javaBin/PollZone/schematic-v5/pdf/pollbox-Layout.pdf

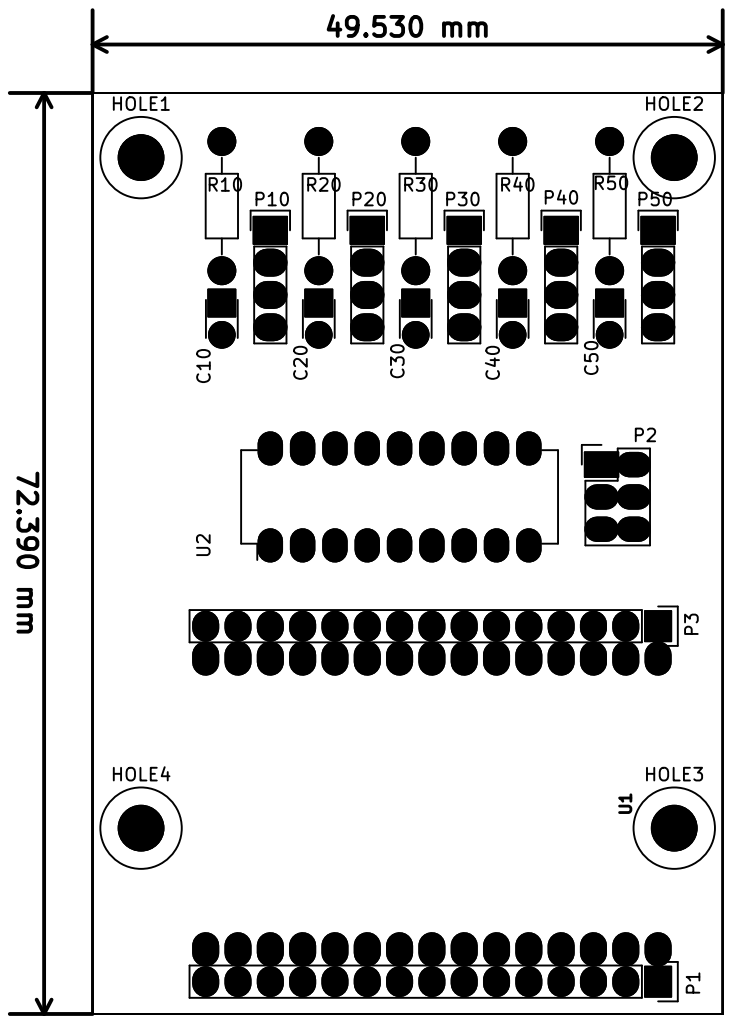
[picture p12: page 1]
