javaBin/PollZone/schematic-v4/pdf/pollbox-Assembly.pdf

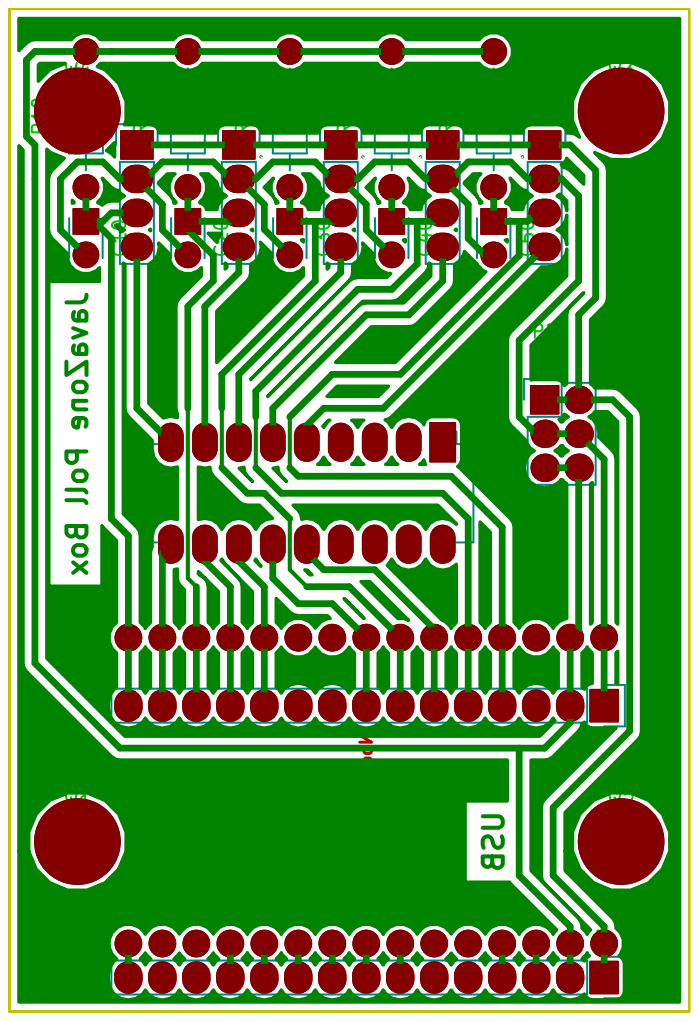
[picture p13: page 1]
