javaBin/PollZone/schematic-v4/pdf/pollbox-AssyOutlinesTop.pdf

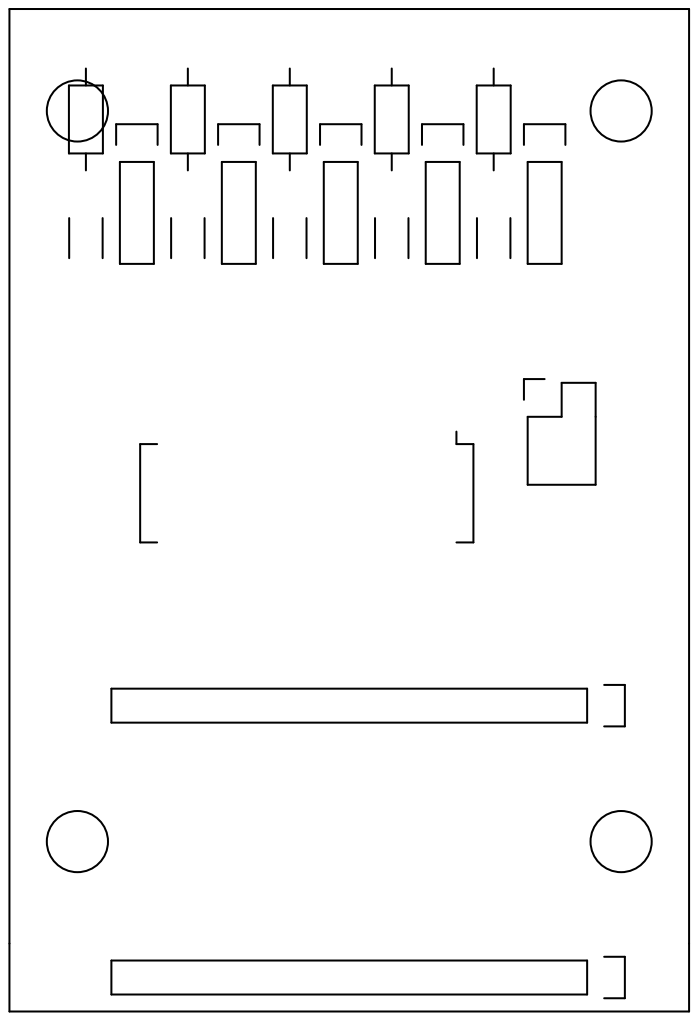
[picture p14: page 1]
