javaBin/PollZone/schematic-v4/pdf/pollbox-AssyTop.pdf

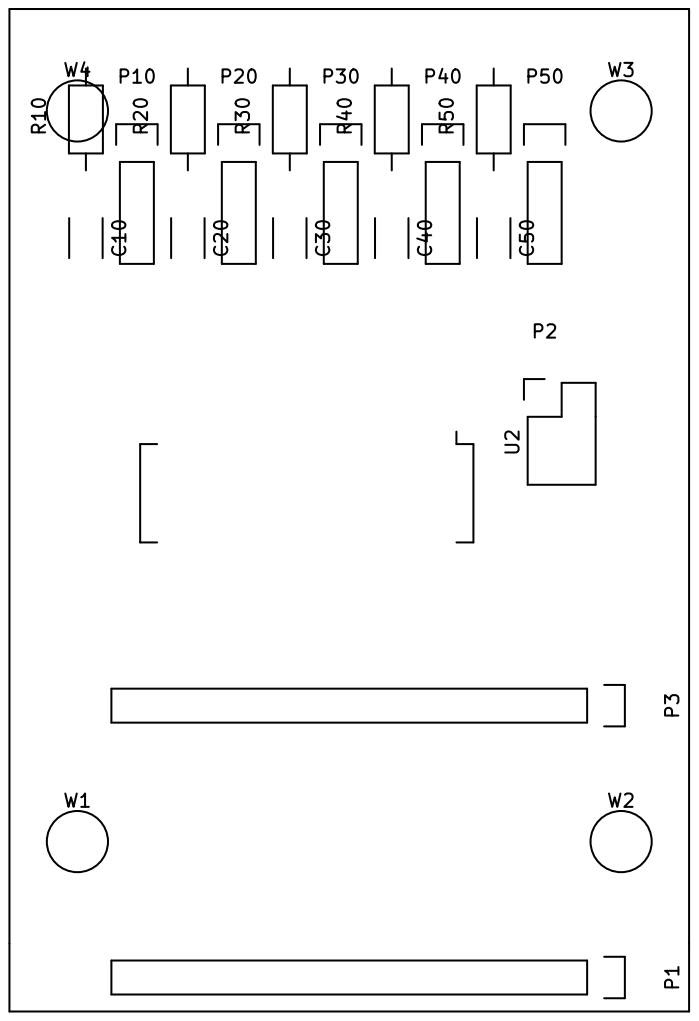
[picture p15: page 1]
