javaBin/PollZone/schematic-v4/pdf/pollbox-B.Cu.pdf

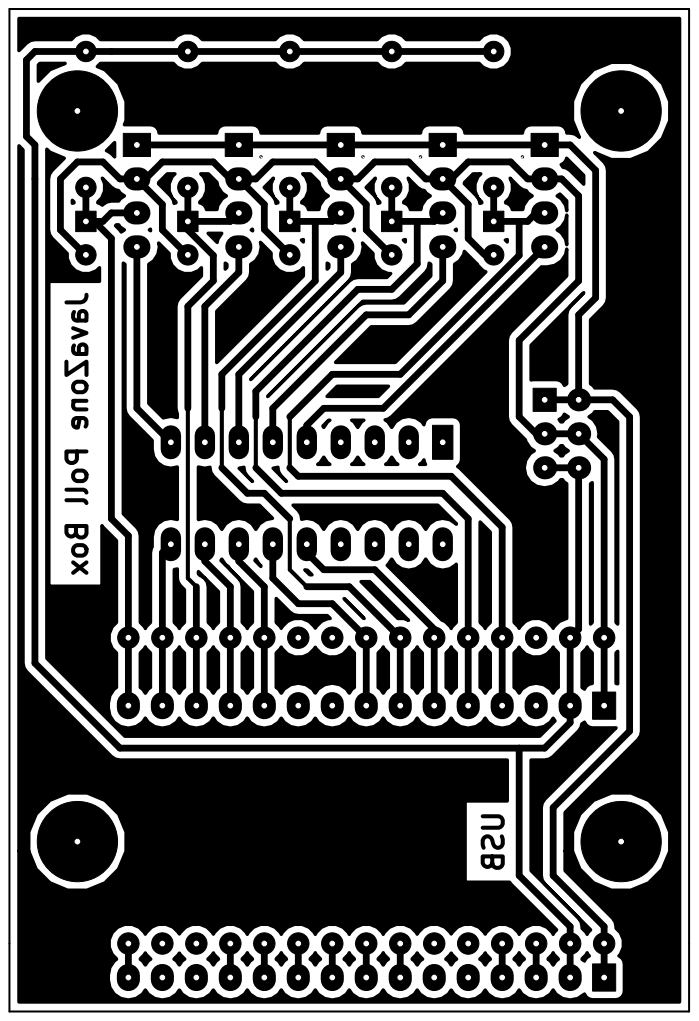
[picture p16: page 1]

USB JavaZone Poll Box
