javaBin/PollZone/schematic-v4/pdf/pollbox-B.Mask.pdf

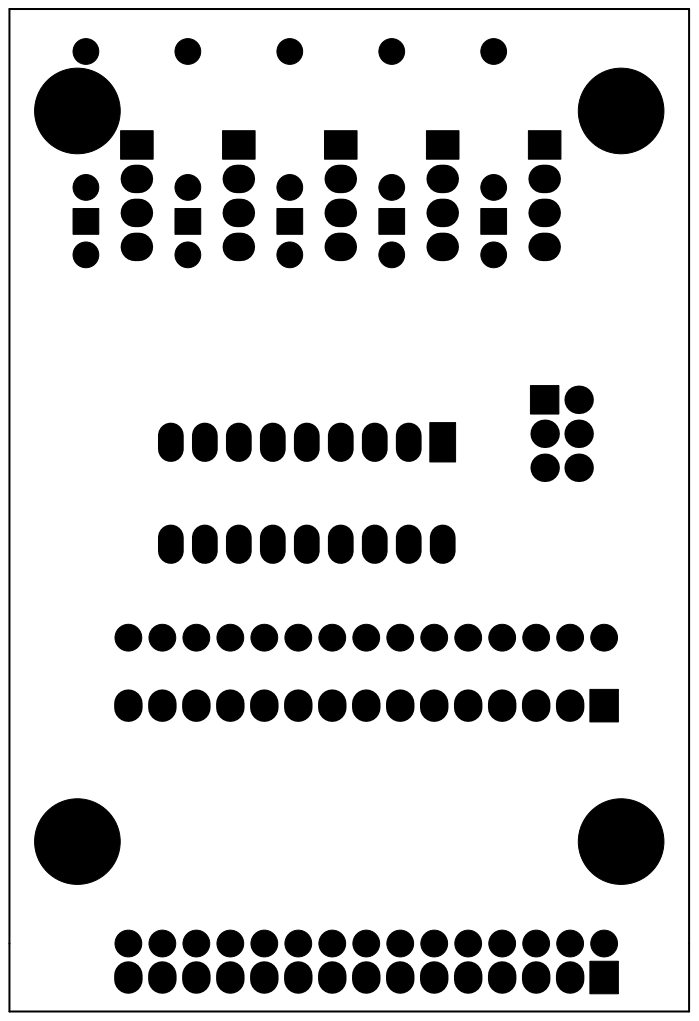
[picture p17: page 1]
