javaBin/PollZone/schematic-v4/pdf/pollbox-B.Silk.pdf

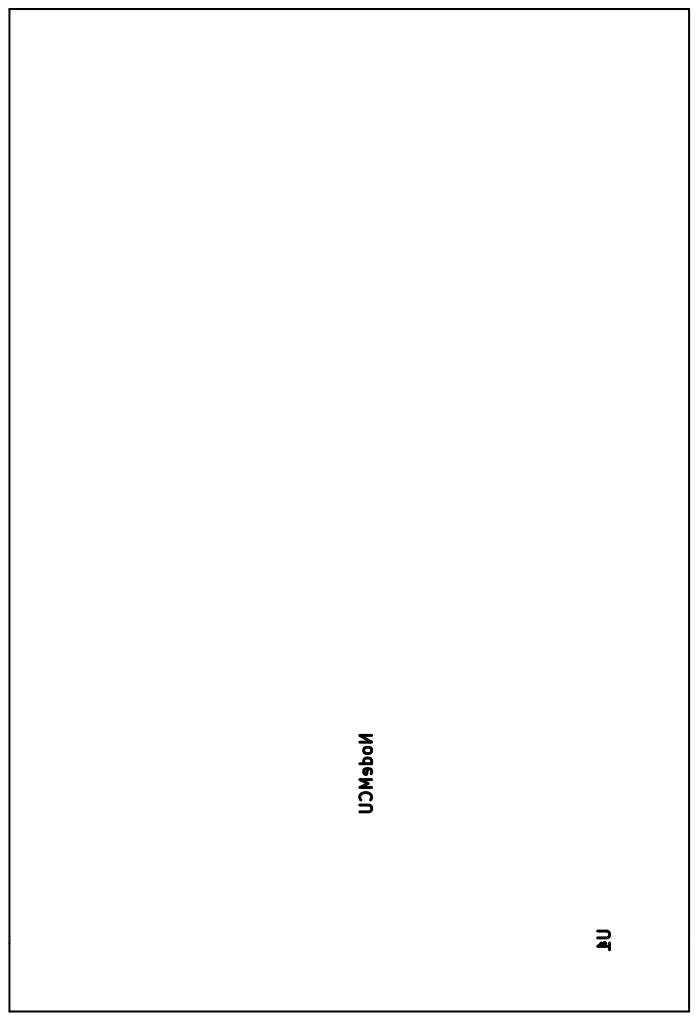
[picture p18: page 1]
