javaBin/PollZone/schematic-v4/pdf/pollbox-Cmts.User.pdf

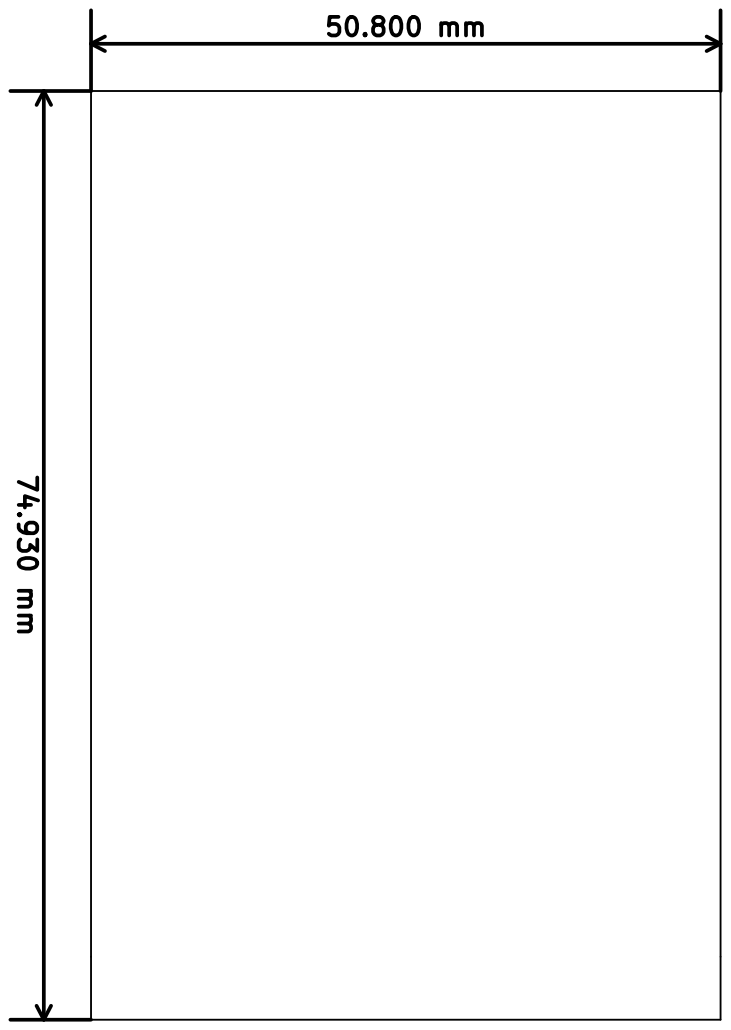
[picture p19: page 1]
