javaBin/PollZone/schematic-v4/pdf/pollbox-F.Cu.pdf

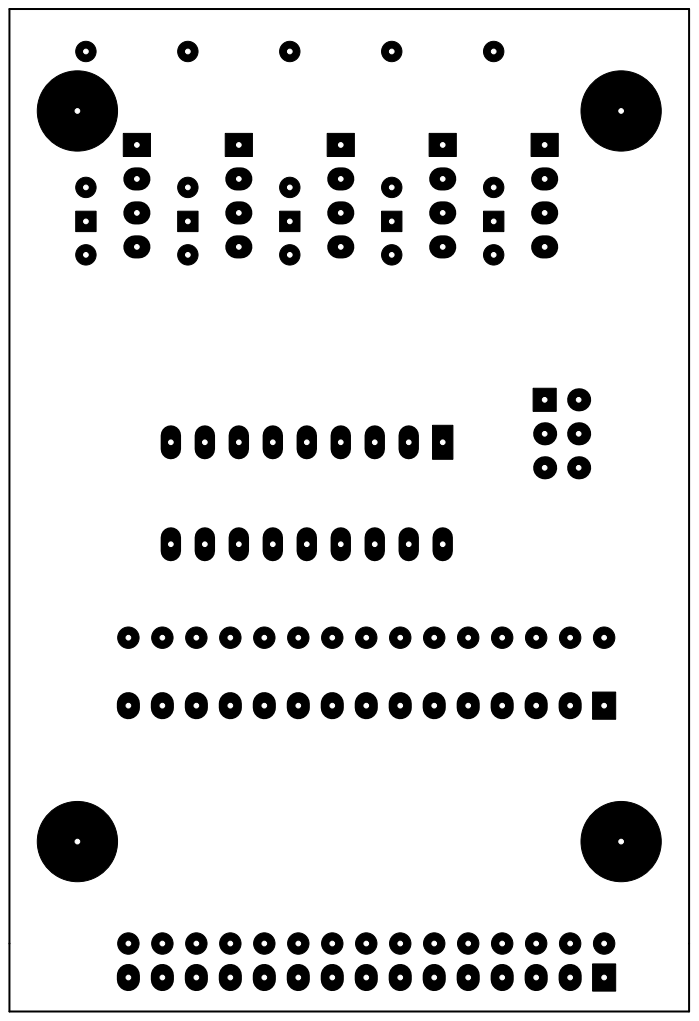
[picture p20: page 1]
