javaBin/PollZone/schematic-v4/pdf/pollbox-Layout.pdf

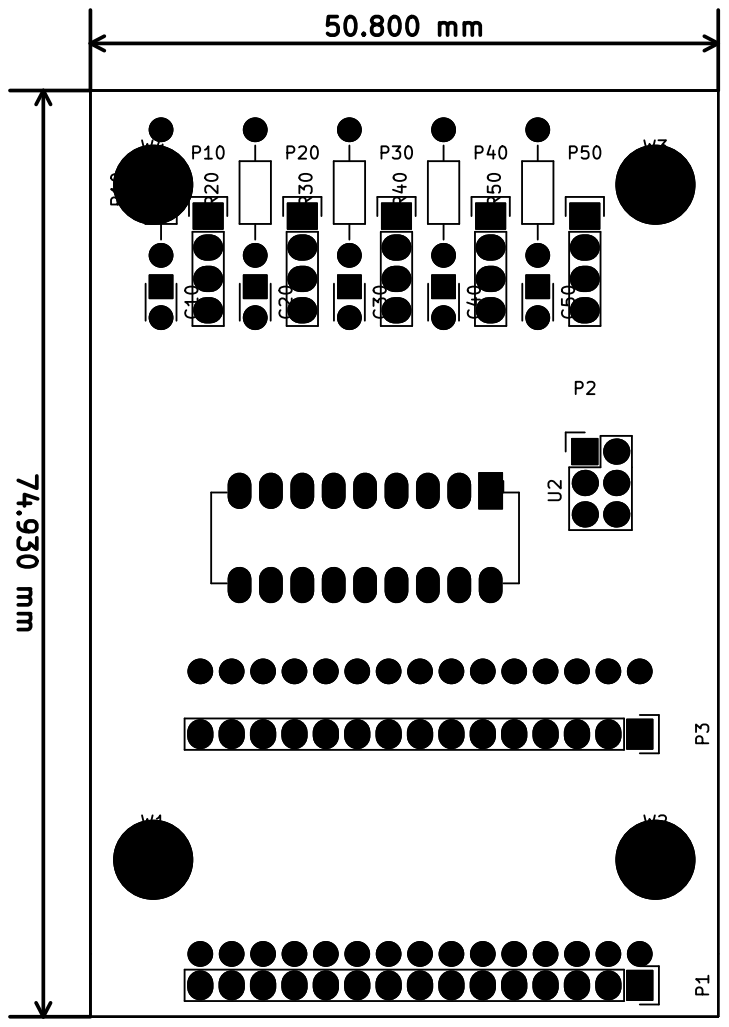
[picture p21: page 1]
