javaBin/PollZone/PollZone/config.h

#pragma once

// Remove comments and give a proper value for these settings:

// #define defaultWifiSsid
// #define defaultWifiPassword
// #define defaultMqttBroker

#ifndef defaultWifiSsid
#error You have to #define defaultWifiSsid
#endif

#ifndef defaultWifiPassword
#error You have to #define defaultWifiPassword
#endif

#ifndef defaultMqttBroker
#error You have to #define defaultMqttBroker
#endif
