javaBin/PollZone/PollZone/Cfg.h

#pragma once

#include <Arduino.h>

class Cfg {
    void readConfig(const String &key, String &dest, const char* defaultValue);
    void writeConfig(const String& key, const String &value);

  public:
    // The buildTimestamp has to build passed in here to make sure it is always refreshed.
    Cfg(const char* buildTimestamp);

    void loadConfig();

    void setSerial(const String &serial);
    void setName(const String &name);
    void setWifi(const String &ssid, const String &password);
    void setMqttBroker(const String &broker);
    void setOtaPassword(const String &otaPassword);

    String serial;
    String name;
    String mqttBroker;
    String wifiSsid;
    String wifiPassword;
    String otaPassword;
    String buildTimestamp;
};
